phantomdubs/Hapticpadv2/3D Files/STL's/LED Diffuser Ring.STL

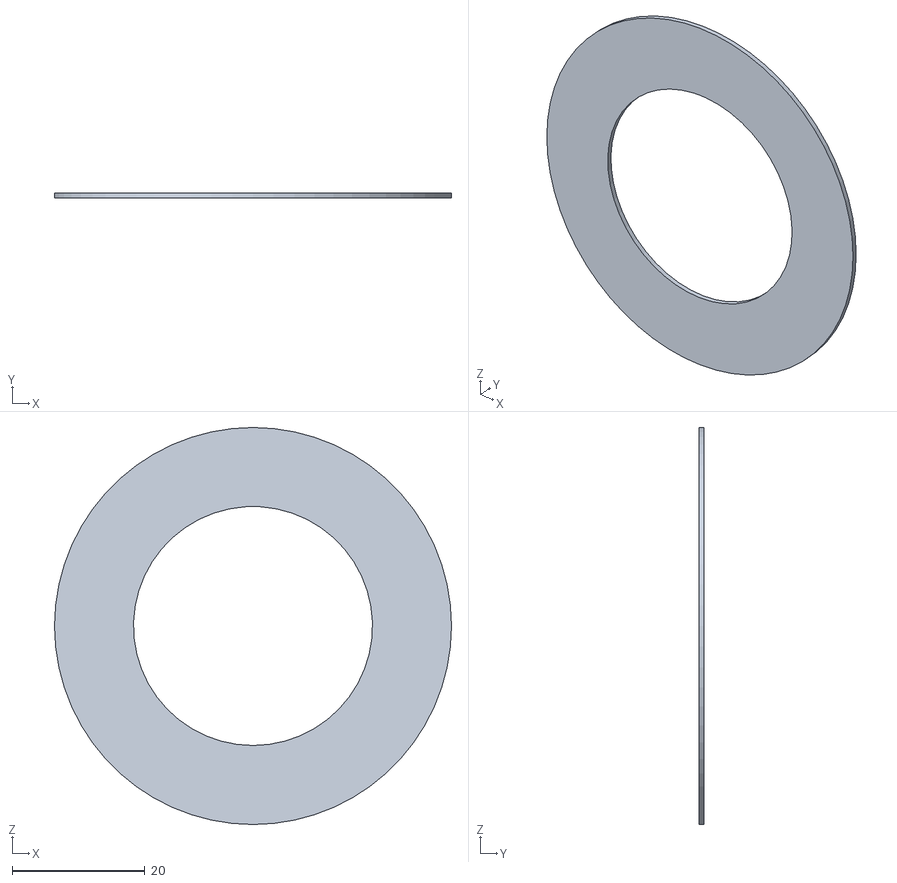
[picture p18: CAD file, 2026-05-03]
3D Files/STL's/LED Diffuser Ring.STL
59.8 x 0.8 x 59.8
